loscorpione/VFO-BFO-HF-ESP32-/VFO-BFO HF ESP32 Code/src/PLL.cpp

#include "si5351.h"
#include "config.h"
#include "modes.h"
#include <Wire.h>

// ============================================
// VARIABILI GLOBALI
// ============================================

Si5351 si5351;

// Calibrazione SI5351
long si5351Calibration = 0;

// Variabili per stato BFO
bool bfoEnabled = false;
unsigned long bfoFrequency = 0;

// Offset pitch per modalità (LSB, USB, CW)
int bfoPitchOffset[3] = {0, 0, 0};
int currentBFOOffset = 0;

// ============================================
// INIZIALIZZAZIONE SI5351
// ============================================

void setupSI5351() {
    if (si5351.init(SI5351_CRYSTAL_LOAD_8PF, 0, 0) == false) {
        while (1) {
            delay(1000);
        }
    }

    si5351.set_pll(SI5351_PLL_FIXED, SI5351_PLLA);
    si5351.drive_strength(SI5351_CLK0, SI5351_DRIVE_8MA);
    si5351.drive_strength(SI5351_CLK1, SI5351_DRIVE_2MA);
    si5351.output_enable(SI5351_CLK0, 1);
    si5351.output_enable(SI5351_CLK1, 0);

    // Applica calibrazione se presente
    if (si5351Calibration != 0) {
        si5351.set_correction(si5351Calibration, SI5351_PLL_INPUT_XO);
    }
}

// ============================================
// AGGIORNAMENTO FREQUENZE VFO E BFO
// ============================================

void updateFrequency() {
    si5351.set_freq(vfoFrequency * 100ULL, SI5351_CLK0);
}

void updateBFO() {
    if (bfoEnabled) {
        si5351.set_freq(bfoFrequency * 100ULL, SI5351_CLK1);
    }
}

// ============================================
// GESTIONE BFO
// ============================================

void enableBFO() {
    bfoEnabled = true;
    si5351.output_enable(SI5351_CLK1, 1);
    updateBFO();
}

void disableBFO() {
    bfoEnabled = false;
    si5351.output_enable(SI5351_CLK1, 0);
}

// ============================================
// CALIBRAZIONE
// ============================================

void calibrateSI5351(long calibration_factor) {
    si5351Calibration = calibration_factor;
    
    // Applica la correzione al cristallo
    si5351.set_correction(calibration_factor, SI5351_PLL_INPUT_XO);
    
    // Forza il riavvio del PLL per applicare la correzione
    si5351.set_pll(SI5351_PLL_FIXED, SI5351_PLLA);
    
    // Riapplica le frequenze
    updateFrequency();
    if (bfoEnabled) {
        updateBFO();
    }
    
    Serial.print("SI5351 calibrato con fattore: ");
    Serial.println(calibration_factor);
}
