loscorpione/VFO-BFO-HF-ESP32-/VFO-BFO HF ESP32 Code/test/src_BKUP_OK/PLL.cpp

#include "si5351.h"
#include "config.h"
#include "modes.h"
#include <Wire.h>

Si5351 si5351;


// Variabili per stato BFO
bool bfoEnabled = false;
unsigned long bfoFrequency = 0;

// Offset pitch per ogni modalità (LSB, USB, CW)
int bfoPitchOffset[3] = {0, 0, 0}; // Inizialmente zero
int currentBFOOffset = 0;


void setupSI5351() {
  Wire.begin(I2C_SDA, I2C_SCL);
  delay(100);

  if (si5351.init(SI5351_CRYSTAL_LOAD_8PF, 0, 0) == false) {
    while(1) {
      delay(1000);
    }
  }

  si5351.set_pll(SI5351_PLL_FIXED, SI5351_PLLA);
  si5351.drive_strength(SI5351_CLK0, SI5351_DRIVE_8MA);
  si5351.drive_strength(SI5351_CLK1, SI5351_DRIVE_8MA);
  si5351.output_enable(SI5351_CLK0, 1);
  si5351.output_enable(SI5351_CLK1, 0); 
}

// Aggiorna frequenza VFO
void updateFrequency() {
  si5351.set_freq(vfoFrequency * 100ULL, SI5351_CLK0);
}

// Aggiorna frequenza BFO
void updateBFO() {
  if (bfoEnabled) {
    si5351.set_freq(bfoFrequency * 100ULL, SI5351_CLK1);
  }
}

// Abilita BFO
void enableBFO() {
  bfoEnabled = true;
  si5351.output_enable(SI5351_CLK1, 1);
  updateBFO();// Aggiorna con l'offset corrente
}
// Disabilita BFO
void disableBFO() {
  bfoEnabled = false;
  si5351.output_enable(SI5351_CLK1, 0);
}
