loscorpione/VFO-BFO-HF-ESP32-/VFO-BFO HF ESP32 Code/test/src_BKUP_OK/modes.h

#ifndef MODES_H
#define MODES_H

enum Mode {
  MODE_AM,
  MODE_LSB,
  MODE_USB,
  MODE_CW,
  MODE_COUNT
};

extern const char* modeNames[];
extern int currentMode;

void changeMode();
void updateModeInfo();
void updateBFOForMode();  

#endif
