loscorpione/VFO-BFO-HF-ESP32-/VFO-BFO HF ESP32 Code/test/src_BKUP_OK/bands.h

#ifndef BANDS_H
#define BANDS_H

struct Band {
  const char* name;
  unsigned long startFreq;
  unsigned long endFreq;
};

extern Band bands[];
extern int currentBandIndex;
extern int totalBands;

int getBandIndex(unsigned long freq);
void changeBand();
void updateBandInfo();

#endif
